TeoPana/TSC_PROJECT/Images/Screenshot 2026-04-21 045548.png

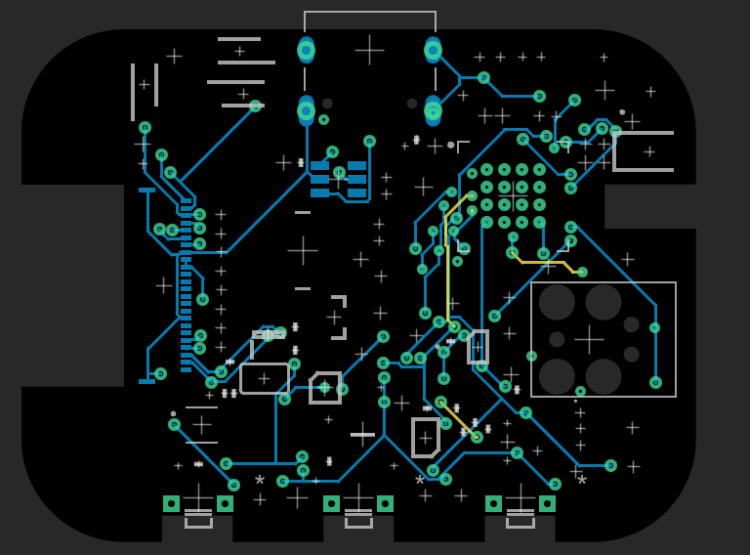
Images/Screenshot 2026-04-21 045548.png
